iotacademy/marvin/Hardware/Layout/bottomview.JPG

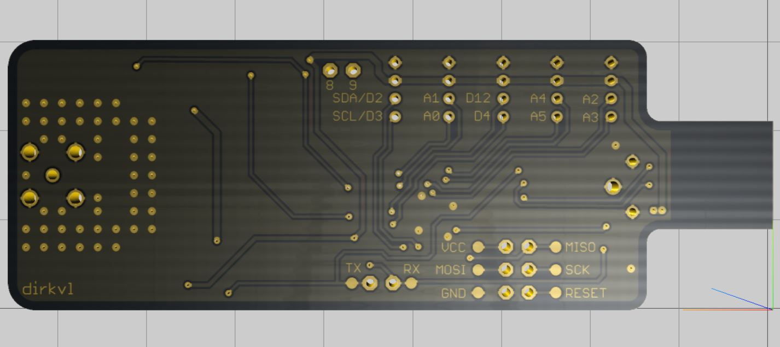
Hardware/Layout/bottomview.JPG
