iotacademy/marvin/Hardware/Layout/Layout.png

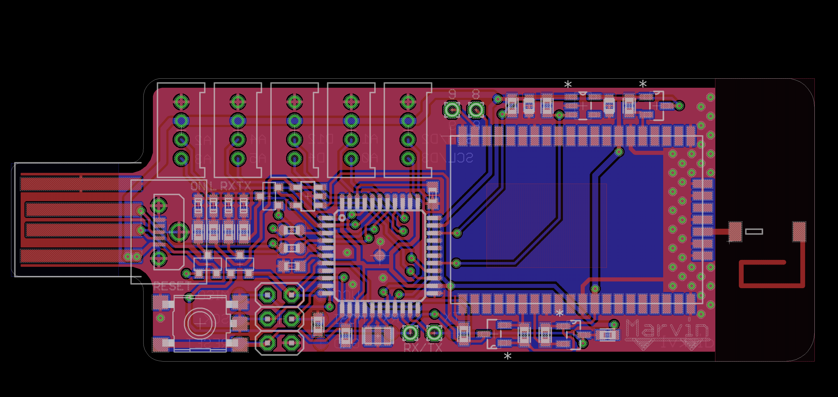
Hardware/Layout/Layout.png
