iotacademy/marvin/Hardware/Layout/topview.JPG

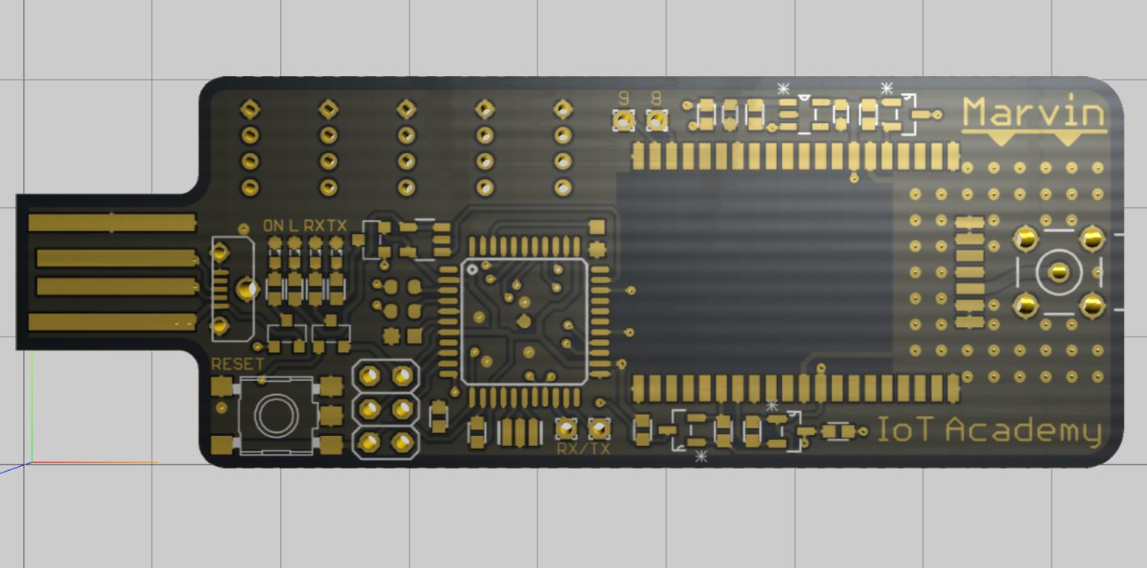
Hardware/Layout/topview.JPG
