iotacademy/marvin/Hardware/Pictures/Antenna.JPG

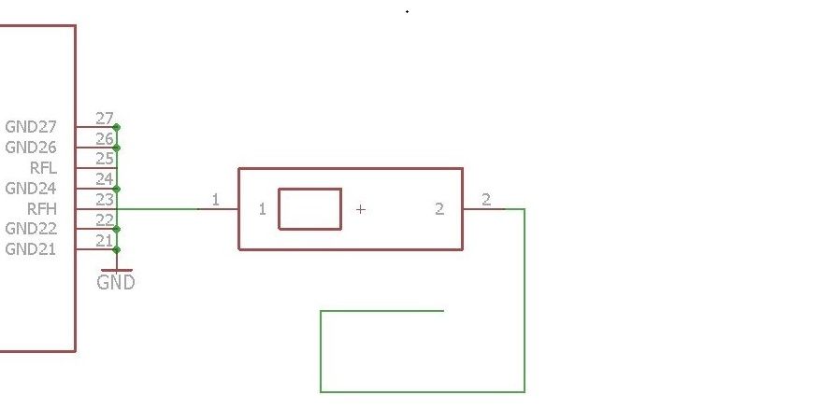
Hardware/Pictures/Antenna.JPG
