iotacademy/marvin/Hardware/Pictures/Dimensions.JPG

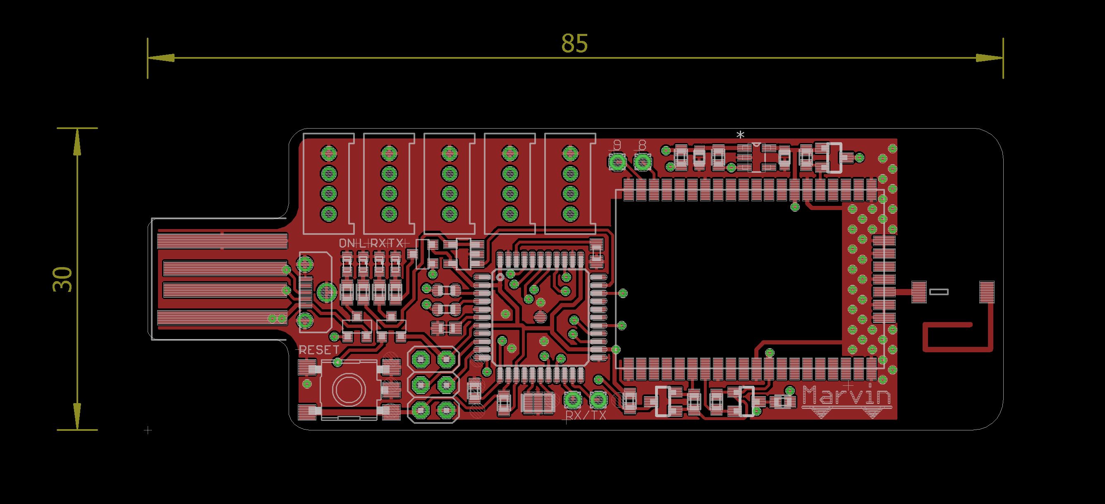
Hardware/Pictures/Dimensions.JPG
