iotacademy/marvin/Hardware/Pictures/Grove.JPG

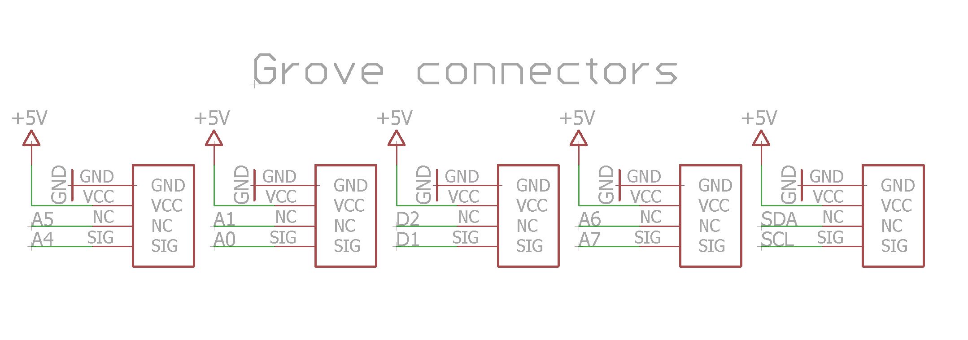
Hardware/Pictures/Grove.JPG
