iotacademy/marvin/Hardware/Pictures/marvin-on-wood.jpg

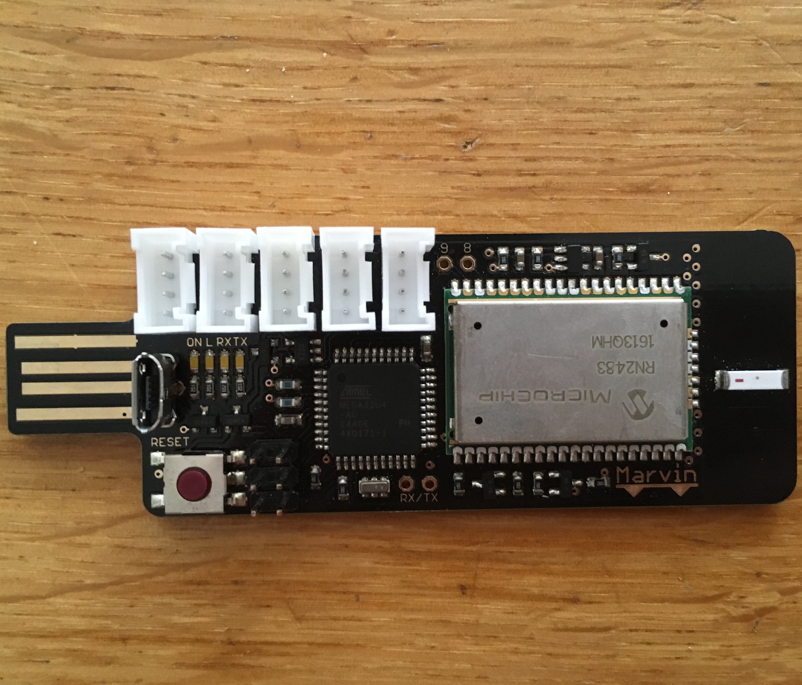
Hardware/Pictures/marvin-on-wood.jpg
