iotacademy/marvin/Hardware/Pictures/MarvinPhoto.png

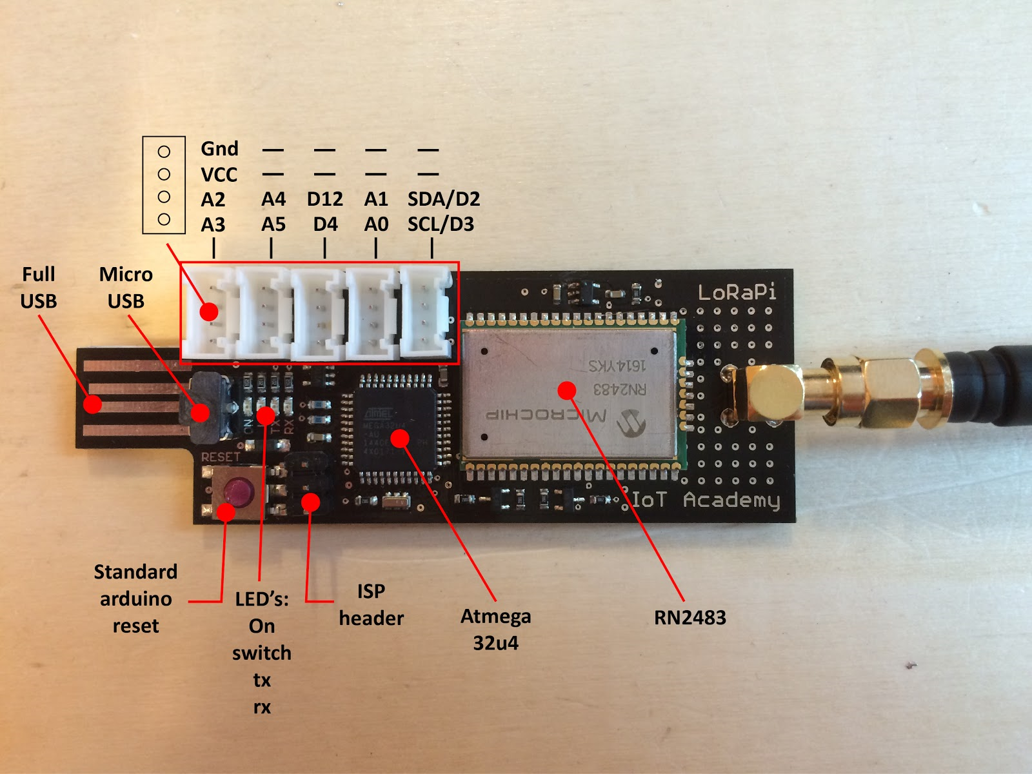
Hardware/Pictures/MarvinPhoto.png
