iotacademy/marvin/Hardware/Pictures/RN2483GPIO.JPG

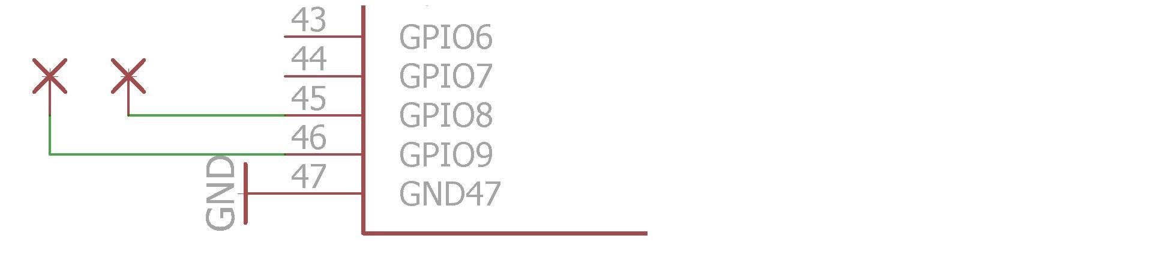
Hardware/Pictures/RN2483GPIO.JPG
