iotacademy/marvin/Software/Pictures/Blinky.jpg

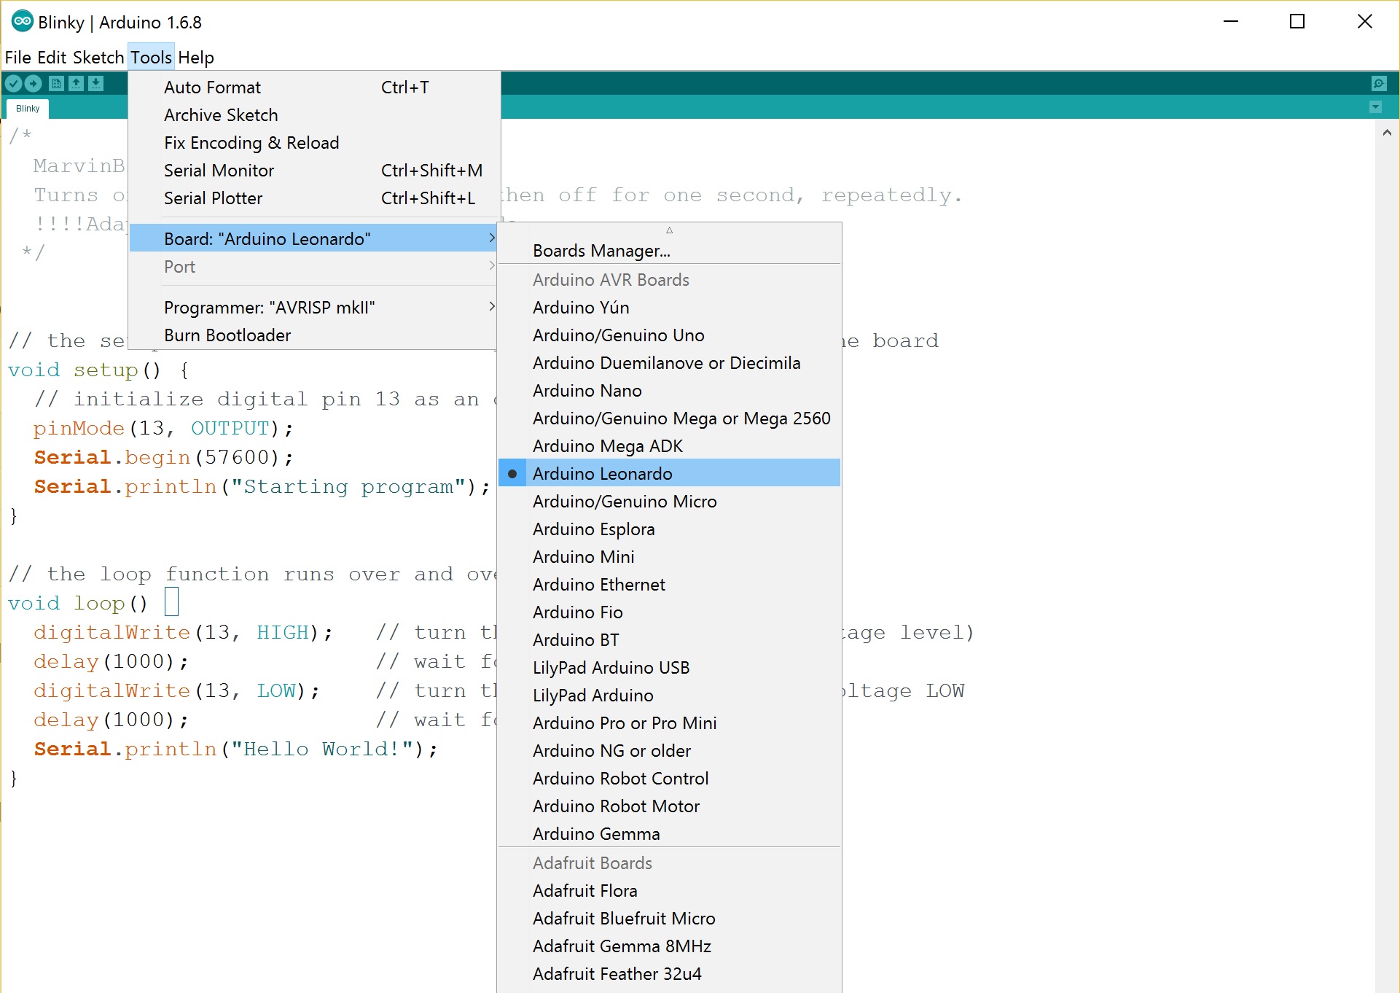
Software/Pictures/Blinky.jpg
