iotacademy/marvin/Software/Pictures/Plugged.jpg

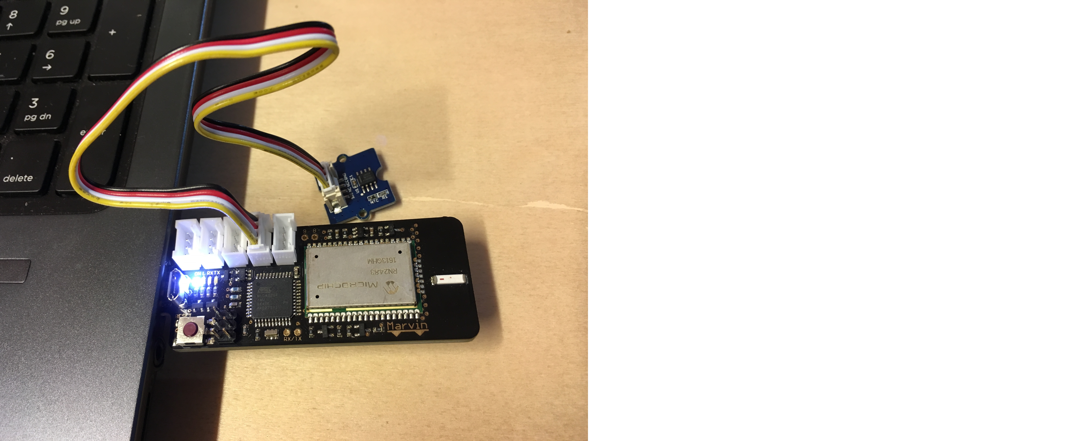
Software/Pictures/Plugged.jpg
