iotacademy/marvin/Software/Pictures/Serial.jpg

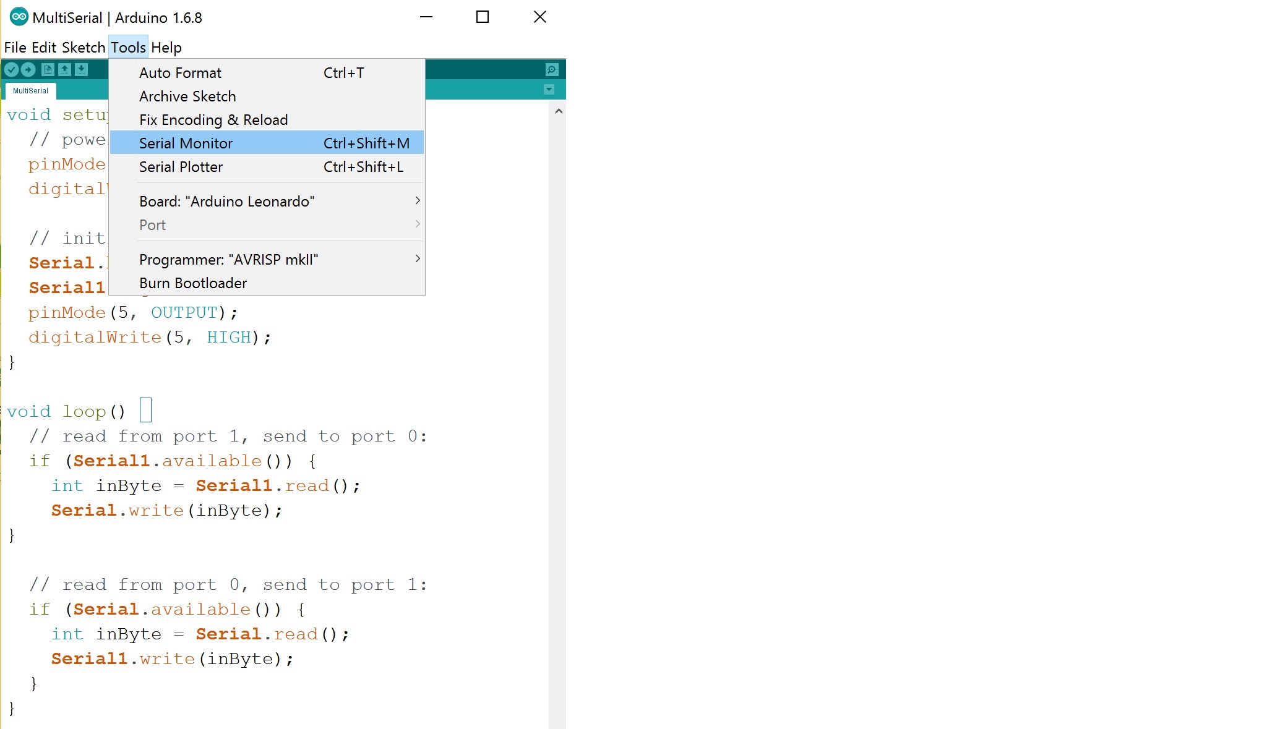
Software/Pictures/Serial.jpg
