iotacademy/marvin/Software/Pictures/Upload.jpg

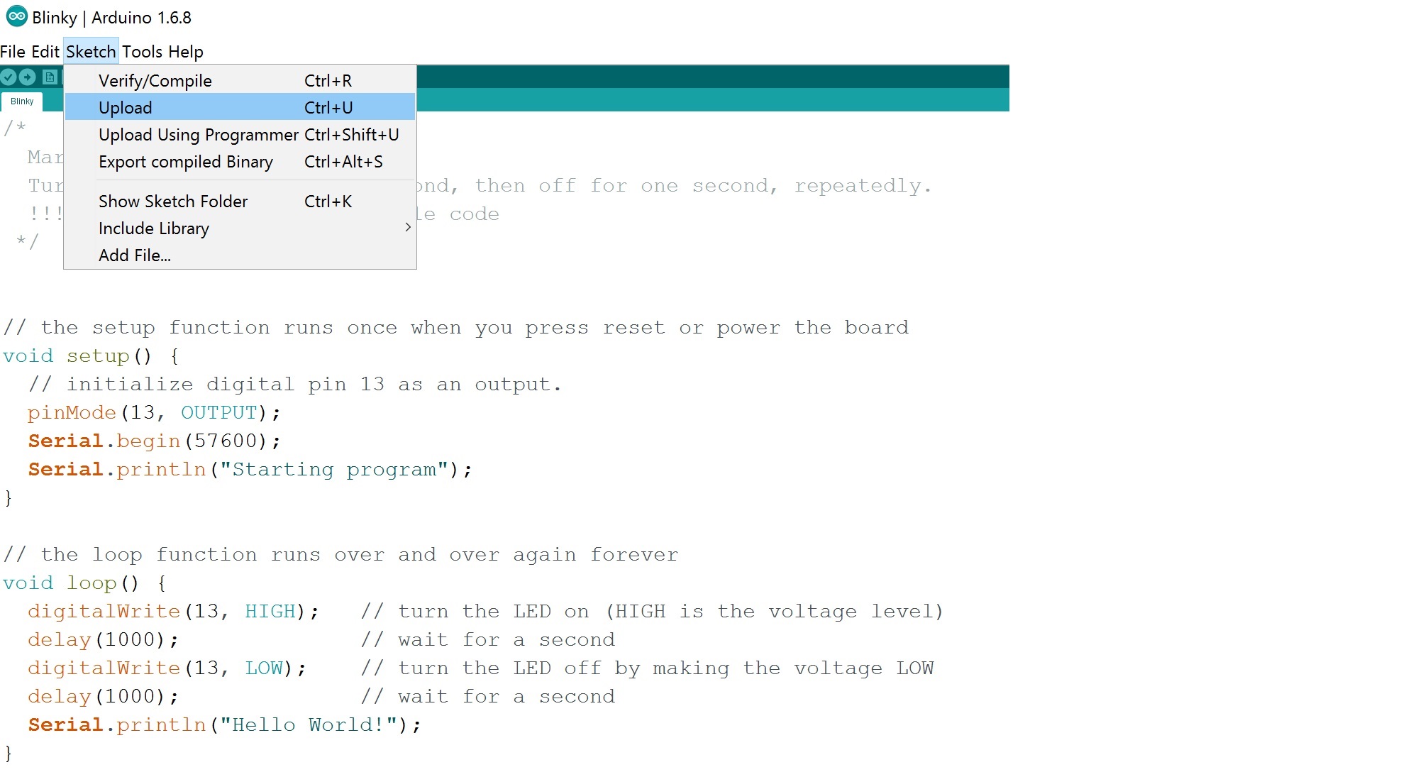
Software/Pictures/Upload.jpg
