iotacademy/marvin/Hardware/Pictures/Marvin_parts.png

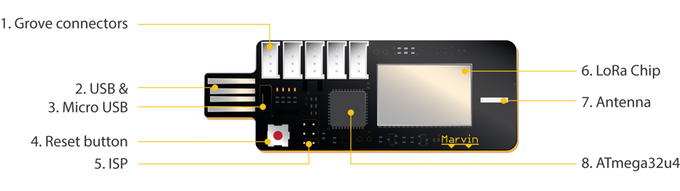
Hardware/Pictures/Marvin_parts.png
